MosheWelcher/cyberdeck-apache3800/parts/lid_panel.scad

// LID screen panel: bezel window + screen retainer bosses + mounting holes.
// Front face (viewing side) is z = panel_t, back face is z = 0.
// Bosses grow from the back (-z); the screen glass sits against the back.
include <../lib/common.scad>

piece = "all";   // "all" (exploded tiles), "whole", or [i, j]

S       = preset(screen, screen_presets);
mod_w   = S[0]; mod_h = S[1]; mod_t = S[2];
act_w   = S[3]; act_h = S[4];
act_off = [S[5], S[6]];

lid_L = case_in_l - 2 * (panel_gap + lid_draft_inset);
lid_W = case_in_w - 2 * (panel_gap + lid_draft_inset);
lid_R = max(case_corner_r - panel_gap - lid_draft_inset, 1);

lid_n  = auto_split(lid_L, lid_W);
lid_xs = resolve_seams(lid_split_x, lid_L, lid_n[0]);
lid_ys = resolve_seams(lid_split_y, lid_W, lid_n[1]);

boss_h     = mod_t + screen_shim;
boss_reach = boss_d / 2 + 0.5;   // boss centre -> screen module edge

function lin(n, len) = n < 1 ? [] : [for (k = [0 : n - 1]) -len/2 + len * (k + 0.5) / n];

// [x, y, angle] — angle points from boss toward the screen (for clips)
function boss_positions() = concat(
    [for (x = lin(bosses_long_side, mod_w))  [x,  mod_h/2 + boss_reach, -90]],
    [for (x = lin(bosses_long_side, mod_w))  [x, -mod_h/2 - boss_reach,  90]],
    [for (y = lin(bosses_short_side, mod_h)) [ mod_w/2 + boss_reach, y, 180]],
    [for (y = lin(bosses_short_side, mod_h)) [-mod_w/2 - boss_reach, y,   0]]
);

// Fit checks: bosses inside the panel; lid posts clear of the monitor and bosses.
// Post footprint is lid_bracket_size [along wall, away from wall]; a hole nearer
// a long wall (|y| side) runs along X.
function post_half(p) = abs(p[1]) / lid_W > abs(p[0]) / lid_L
    ? [lid_bracket_size[0], lid_bracket_size[1]] / 2
    : [lid_bracket_size[1], lid_bracket_size[0]] / 2;
function overlaps(c1, h1, c2, h2) =
    abs(c1[0] - c2[0]) < h1[0] + h2[0] && abs(c1[1] - c2[1]) < h1[1] + h2[1];
for (b = boss_positions()) {
    c = [b[0] + screen_offset[0], b[1] + screen_offset[1]];
    assert(abs(c[0]) + boss_d / 2 <= lid_L / 2 && abs(c[1]) + boss_d / 2 <= lid_W / 2,
           str("screen boss at ", c, " sticks out of the lid panel — monitor too big for this boss layout"));
    for (p = lid_mount_holes)
        assert(!overlaps(c, [boss_d, boss_d] / 2, p, post_half(p)),
               str("screen boss at ", c, " hits the lid post at ", p));
}
for (p = lid_mount_holes)
    assert(!overlaps(screen_offset, [mod_w, mod_h] / 2, p, post_half(p)),
           str("lid post at ", p, " sits under the monitor — remove/move it in lid_mount_holes"));
// Monitor vs. the lid walls at its back face (the walls lean in with depth).
mon_back_depth = lid_panel_drop + panel_t + screen_shim + mod_t;
mon_gap = [case_in_l / 2 - lid_wall_draft * mon_back_depth - mod_w / 2 - abs(screen_offset[0]),
           case_in_w / 2 - lid_wall_draft * mon_back_depth - mod_h / 2 - abs(screen_offset[1])];
echo(str("LID monitor-to-wall gap: ends ", mon_gap[0], " mm, top/bottom ", mon_gap[1], " mm"));
assert(min(mon_gap) > 0, str("monitor does not fit inside the lid walls (gap ", mon_gap, ")"));
assert(mon_back_depth < lid_depth - lid_fillet_r,
       "monitor back reaches the lid's wall-to-floor fillet — check the end clearance");

// Finger notches over the monitor's edge controls: [cx, cy, w, h] rects,
// open through the panel edge. y is measured up from the monitor's bottom edge.
notch_rects = [for (n = lid_notches)
    let(x_in  = n[0] * (mod_w / 2 - notch_over) + screen_offset[0],
        x_out = n[0] * (lid_L / 2 + notch_r + 1),
        y0 = screen_offset[1] - mod_h / 2 + n[1],
        y1 = screen_offset[1] - mod_h / 2 + n[2])
    [(x_in + x_out) / 2, (y0 + y1) / 2, abs(x_out - x_in), y1 - y0]];
for (r = notch_rects)
    assert(r[1] - r[3] / 2 > -mod_h / 2 + screen_offset[1] && r[1] + r[3] / 2 < mod_h / 2 + screen_offset[1],
           "finger notch runs past the monitor's end — check lid_notches");

// Seam screws stay out of the window (+ bevel + head), from under the monitor
// (the back-side nut would hold it off the panel) and away from mounts/bosses.
win_c = screen_offset + act_off;
nut_d = m3_nut_af / cos(30);
lid_keepouts = concat(
    [[win_c[0], win_c[1],
      act_w + 2 * (window_margin + window_chamfer) + m3_csk_d + 2,
      act_h + 2 * (window_margin + window_chamfer) + m3_csk_d + 2]],
    [[screen_offset[0], screen_offset[1], mod_w + nut_d + 1, mod_h + nut_d + 1]],
    point_keepouts(lid_mount_holes),
    point_keepouts([for (b = boss_positions()) [b[0] + screen_offset[0], b[1] + screen_offset[1]]], boss_d + 8),
    [for (r = notch_rects) [r[0], r[1], r[2] + m3_csk_d + 2, r[3] + m3_csk_d + 2]]
);

module viewing_window() {
    ww = act_w + 2 * window_margin;
    wh = act_h + 2 * window_margin;
    c  = window_chamfer;
    hull() {
        translate([0, 0, -1]) linear_extrude(1 + panel_t - c) rrect(ww, wh, 1);
        translate([0, 0, panel_t + 1]) linear_extrude(0.01) rrect(ww + 2 * (c + 1), wh + 2 * (c + 1), 2 + c);
    }
}

module lid_panel_whole() {
    insert_depth = min(m3_insert_depth, boss_h + panel_t - 1.2);
    difference() {
        union() {
            plate(lid_L, lid_W, lid_R, panel_t);
            translate(screen_offset)
                for (b = boss_positions())
                    translate([b[0], b[1], -boss_h]) cylinder(d = boss_d, h = boss_h + 0.01);
        }
        translate(screen_offset + act_off) viewing_window();
        for (r = notch_rects)
            translate([r[0], r[1], -boss_h - 1]) linear_extrude(boss_h + panel_t + 2) rrect(r[2], r[3], notch_r);
        translate(screen_offset)
            for (b = boss_positions())
                translate([b[0], b[1], -boss_h - 0.01]) cylinder(d = m3_insert_d, h = insert_depth);
        for (p = lid_mount_holes) translate(p) m3_csk(panel_t);
        for (p = seam_holes(lid_xs, lid_ys, lid_L, lid_W, lid_keepouts)) translate(p) seam_screw(panel_t);
    }
}

// Screen module stand-in for the assembly preview.
module screen_dummy() {
    translate(concat(screen_offset, [-screen_shim - mod_t]))
        linear_extrude(mod_t) rrect(mod_w, mod_h, 1);
}

tiled(piece, lid_xs, lid_ys, panel_t) lid_panel_whole();
